MCPO-Spartan-117/Ploopy-Mods/Models/Kicad/PR(E,P)C003DAAN-RC.stp

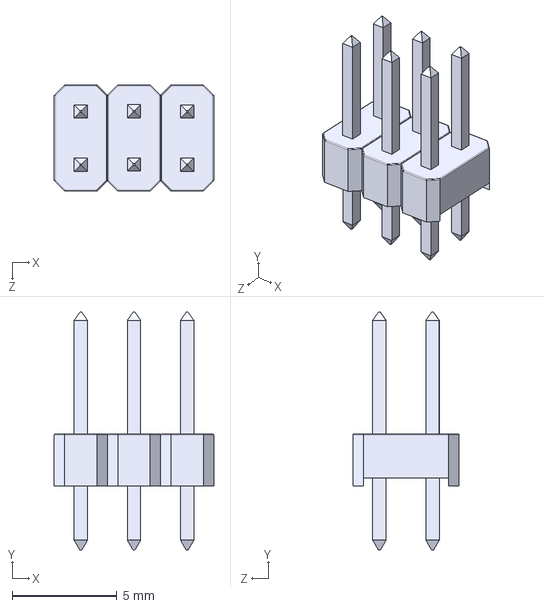
[picture p15: CAD file, 2024-03-17]
Models/Kicad/PR(E,P)C003DAAN-RC.stp
7.62 x 11.4 x 5.08 mm
Dual TH with end bump format x 3
