MCPO-Spartan-117/Ploopy-Mods/Models/Kicad/m20-9990245_asm.stp

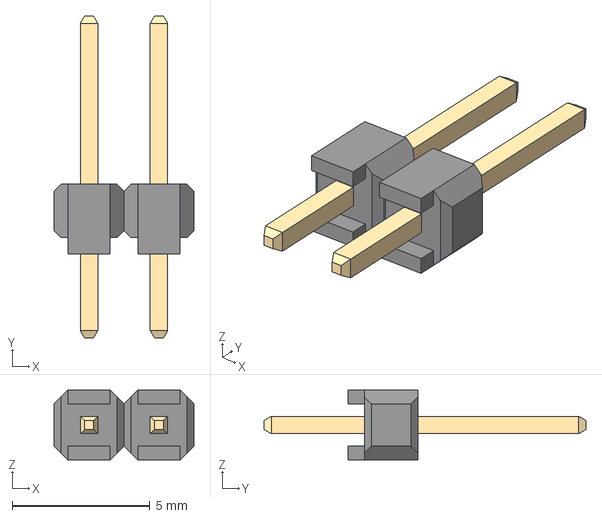
[picture p16: CAD file, 2024-03-17]
Models/Kicad/m20-9990245_asm.stp
5.08 x 11.7 x 2.54 mm
M20-999-MOULD
M20-999-PIN x 2
